brainboxemb/2026-007-01.cad.tool-board/v1.0/cad/project_components/garage_floor.scad

//
// Project component: current garage floor area.
//

include <../components/floor_slab.scad>

module garage_floor(width, depth, thickness) {
    floor_slab(
        width     = width,
        depth     = depth,
        thickness = thickness
    );
}
